Adrian-Amoddio/wildlife-detection-camera-system/object_detection/runs/detect/pi_demo/bird3.jpg

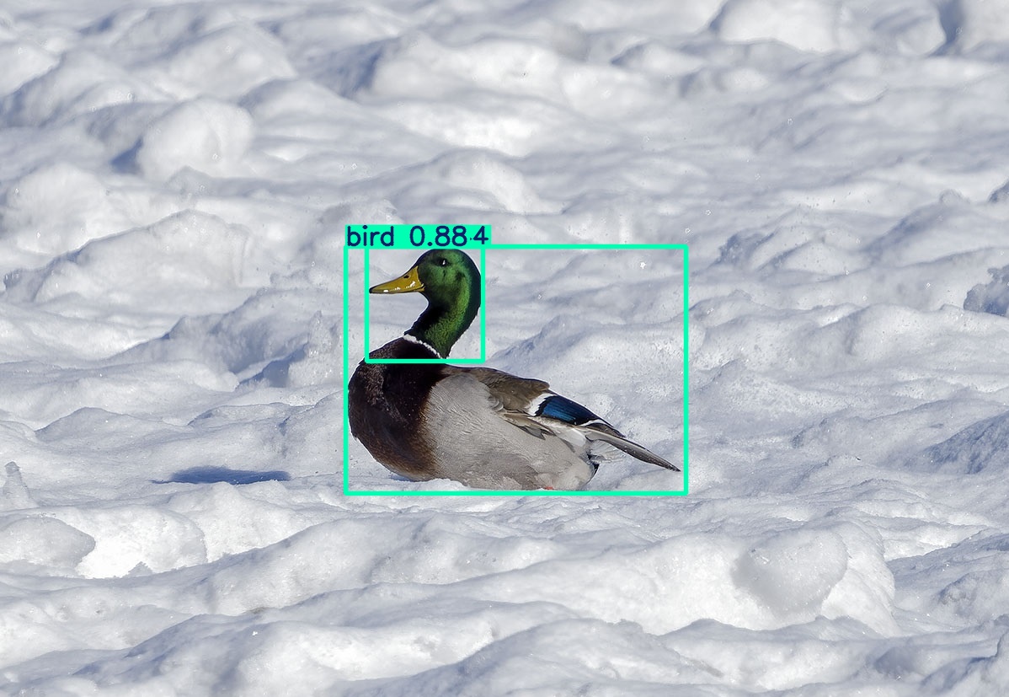
object_detection/runs/detect/pi_demo/bird3.jpg
