Adrian-Amoddio/wildlife-detection-camera-system/object_detection/runs/detect/pi_demo/bird.jpg

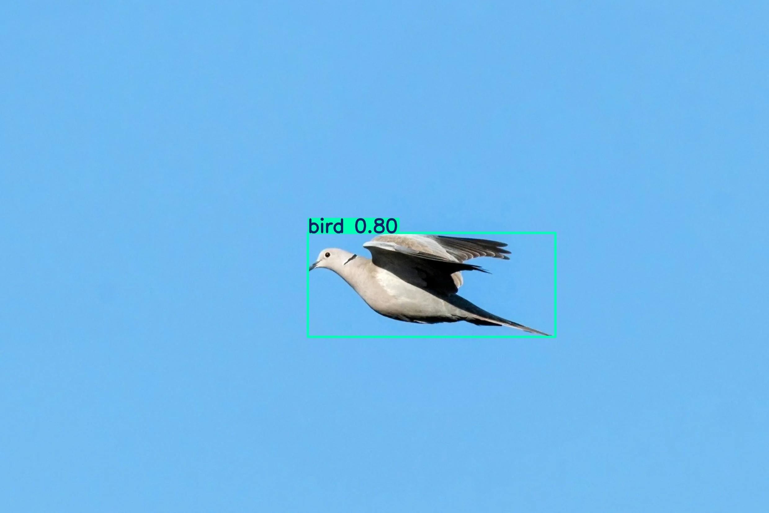
object_detection/runs/detect/pi_demo/bird.jpg
