Adrian-Amoddio/wildlife-detection-camera-system/object_detection/samples/dog.webp

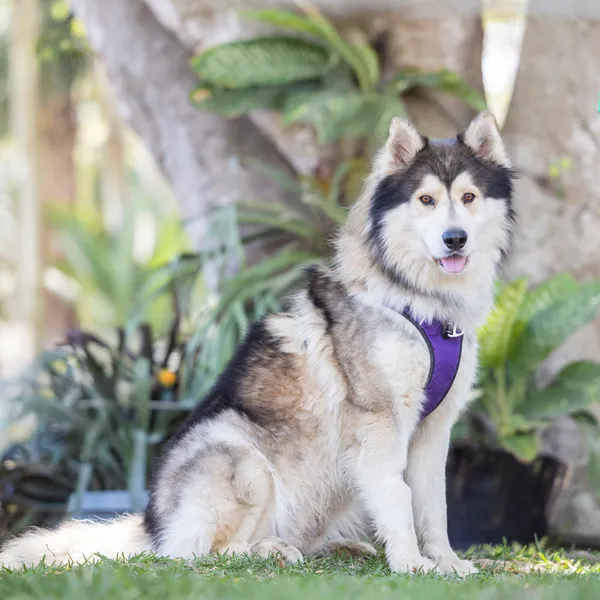
object_detection/samples/dog.webp
