Adrian-Amoddio/wildlife-detection-camera-system/docs/build-images/1.jpg

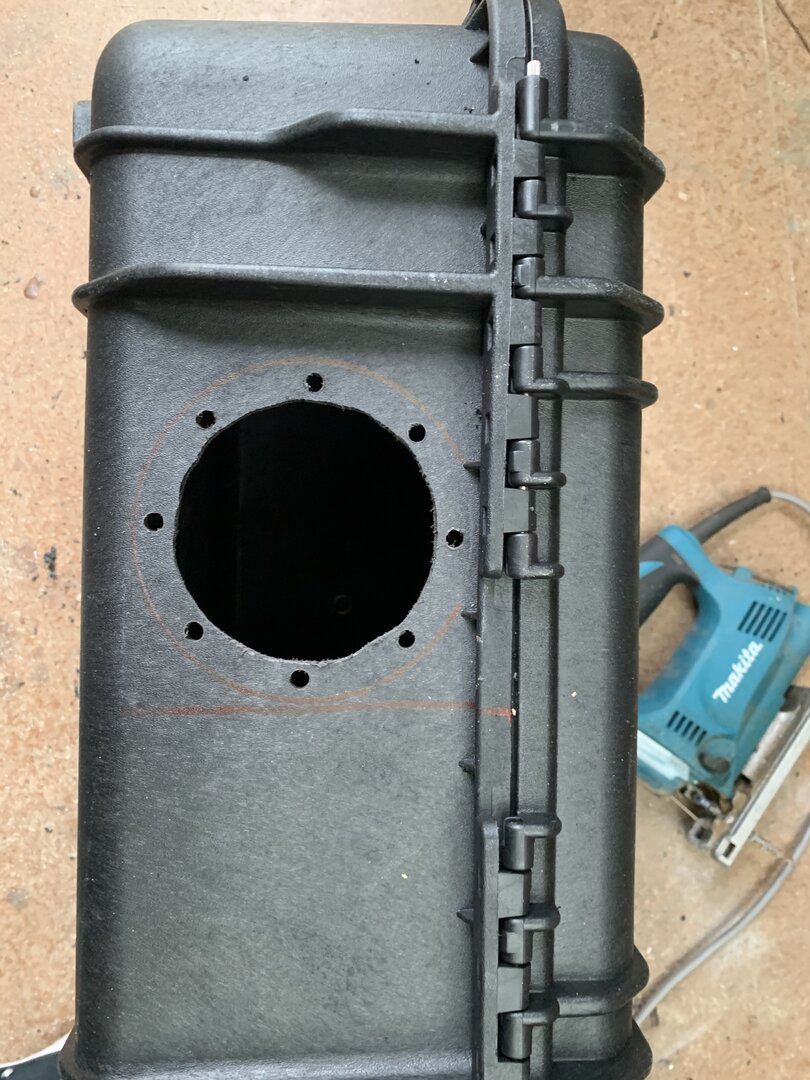
docs/build-images/1.jpg
