Adrian-Amoddio/wildlife-detection-camera-system/docs/build-images/2.jpg

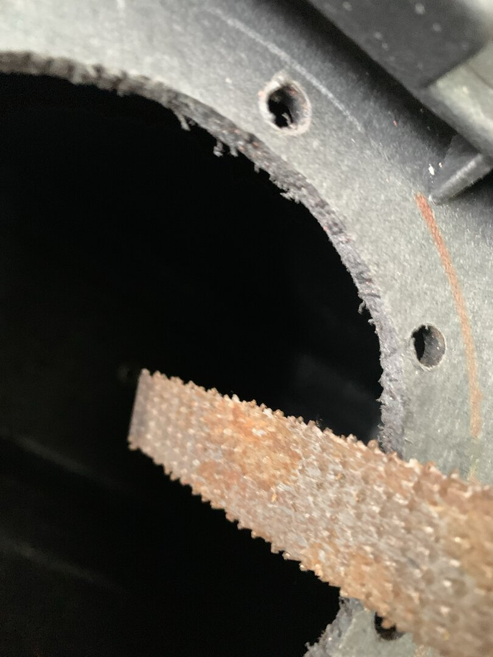
docs/build-images/2.jpg
