Adrian-Amoddio/wildlife-detection-camera-system/docs/build-images/3.jpg

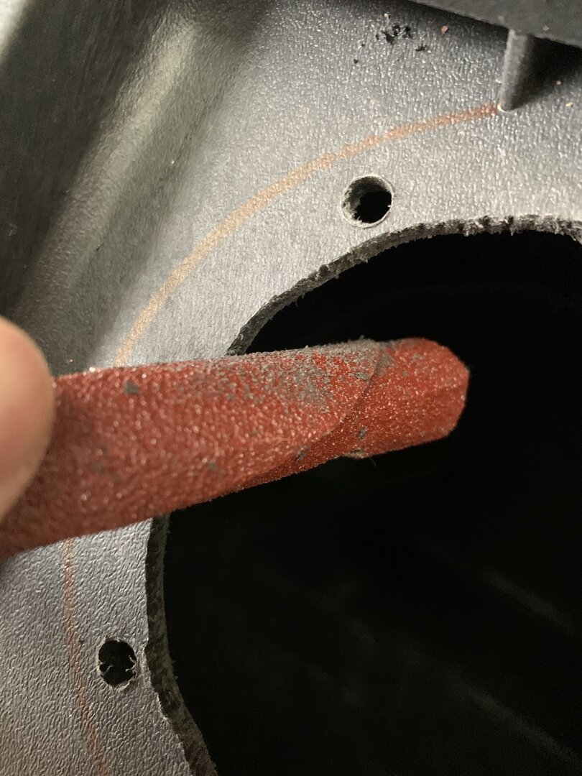
docs/build-images/3.jpg
