Adrian-Amoddio/wildlife-detection-camera-system/docs/build-images/4.jpg

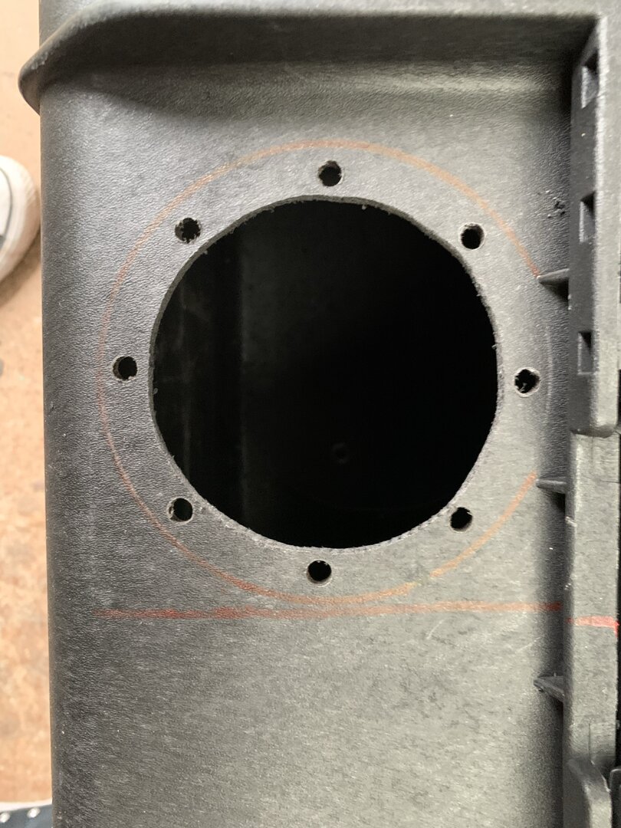
docs/build-images/4.jpg
