Adrian-Amoddio/wildlife-detection-camera-system/docs/build-images/6.jpg

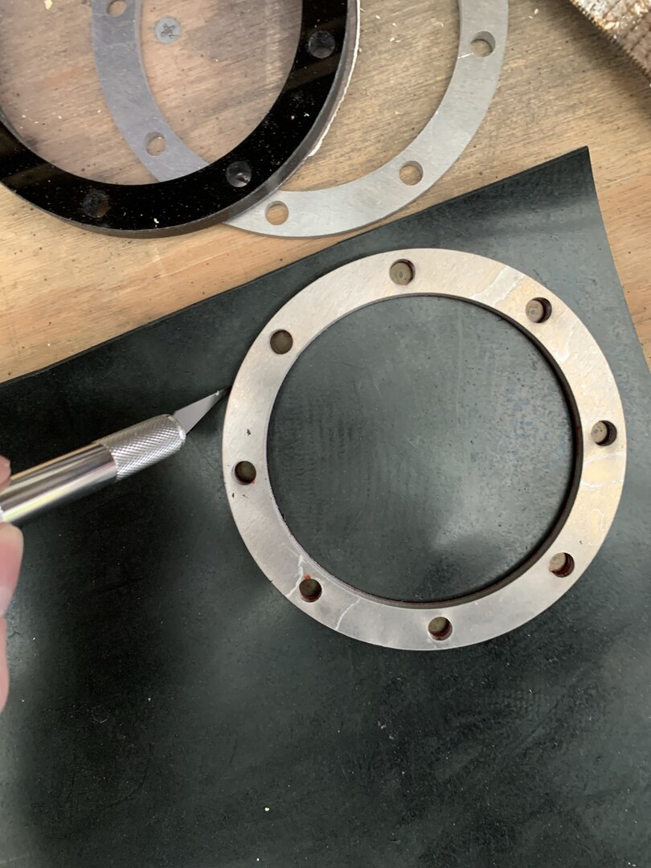
docs/build-images/6.jpg
