Adrian-Amoddio/wildlife-detection-camera-system/docs/build-images/7.jpg

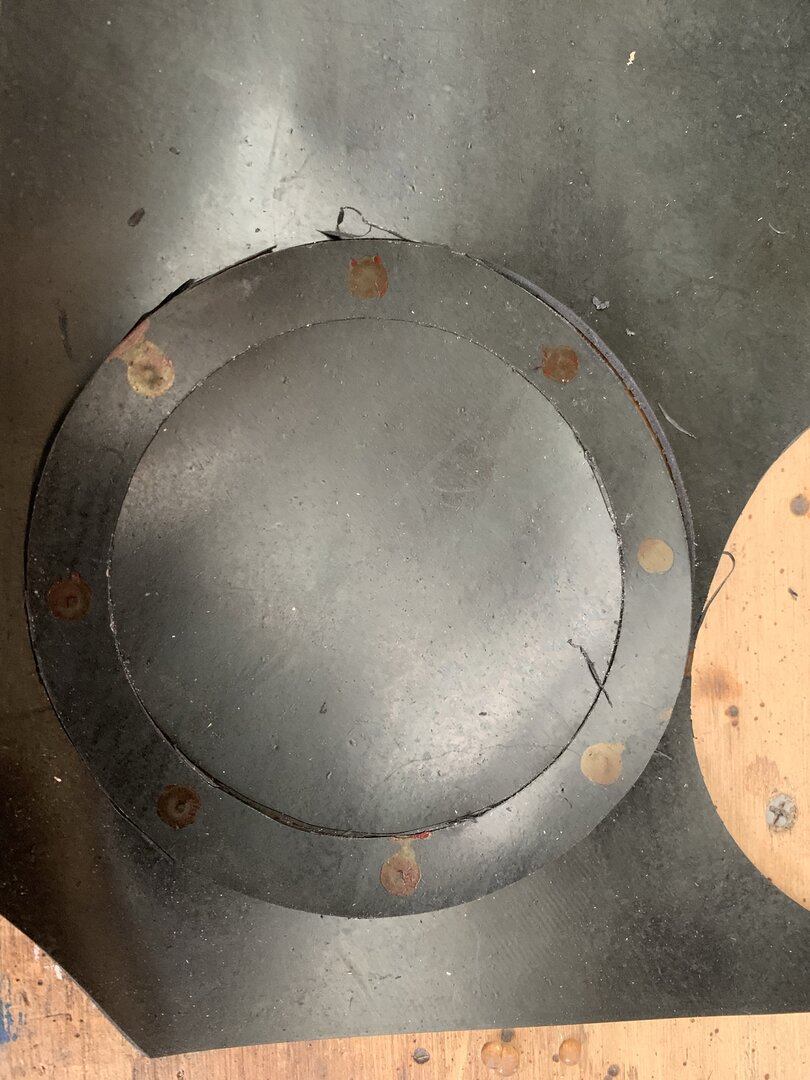
docs/build-images/7.jpg
