Adrian-Amoddio/wildlife-detection-camera-system/docs/build-images/8.jpg

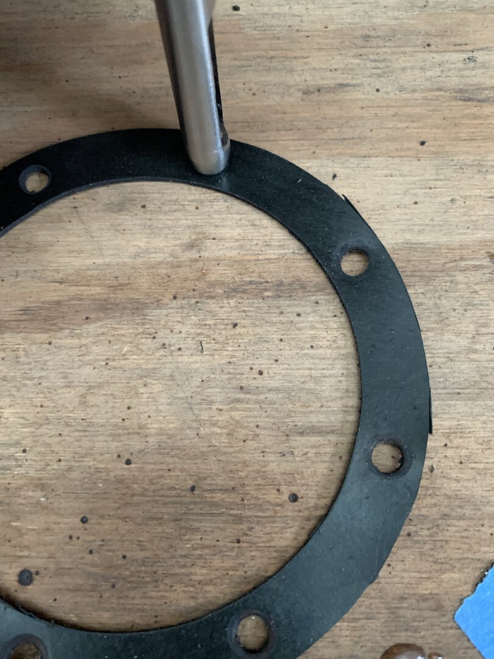
docs/build-images/8.jpg
