Adrian-Amoddio/wildlife-detection-camera-system/docs/build-images/9.jpg

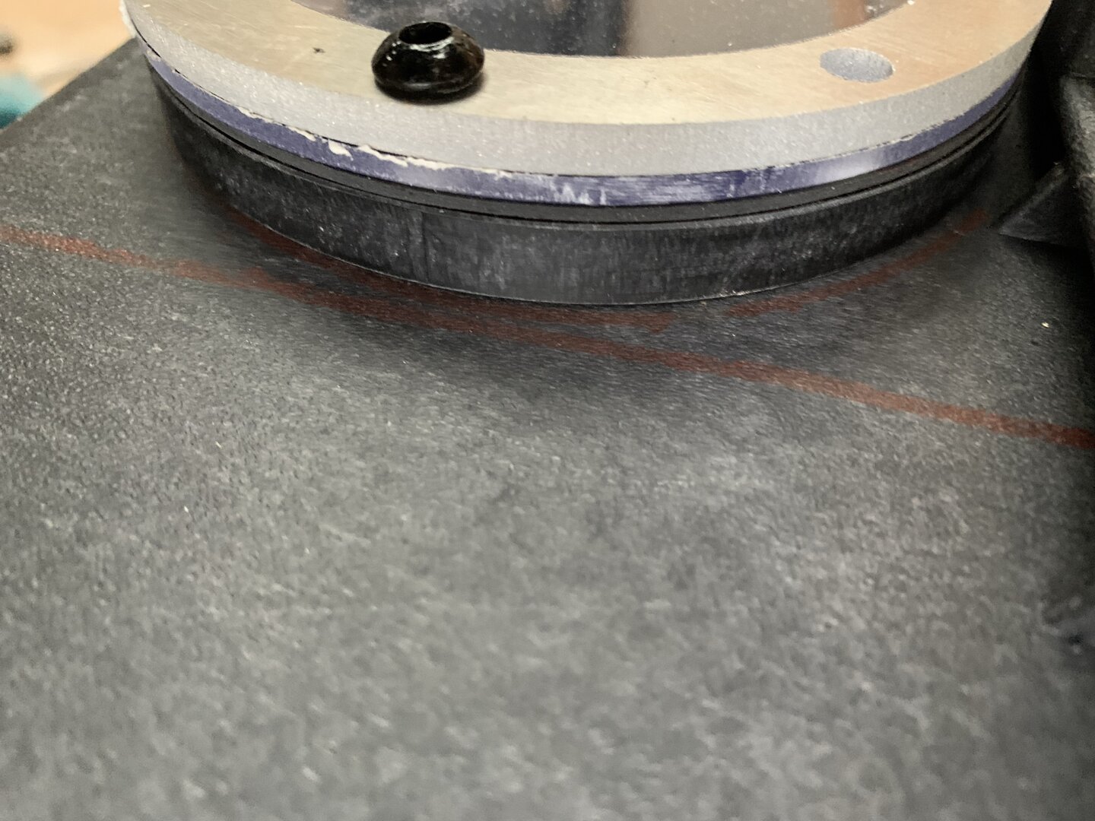
docs/build-images/9.jpg
