Adrian-Amoddio/wildlife-detection-camera-system/docs/build-images/10.jpg

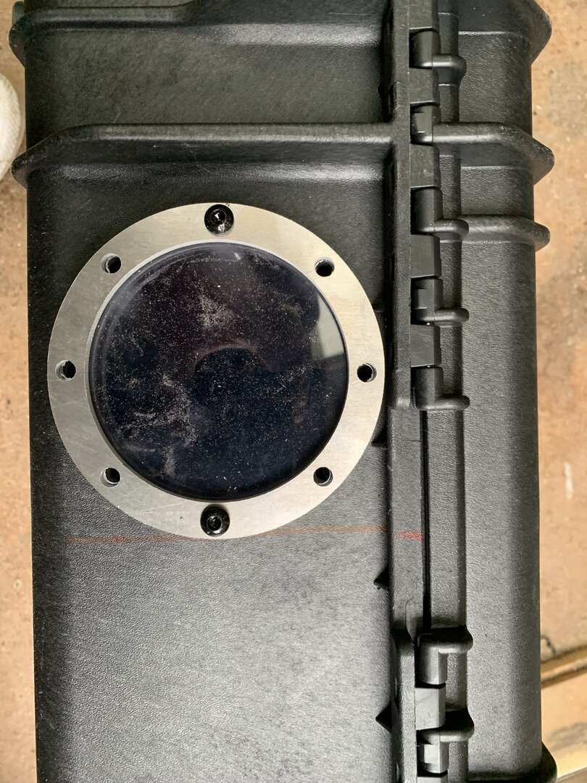
docs/build-images/10.jpg
