Adrian-Amoddio/wildlife-detection-camera-system/docs/build-images/11.jpg

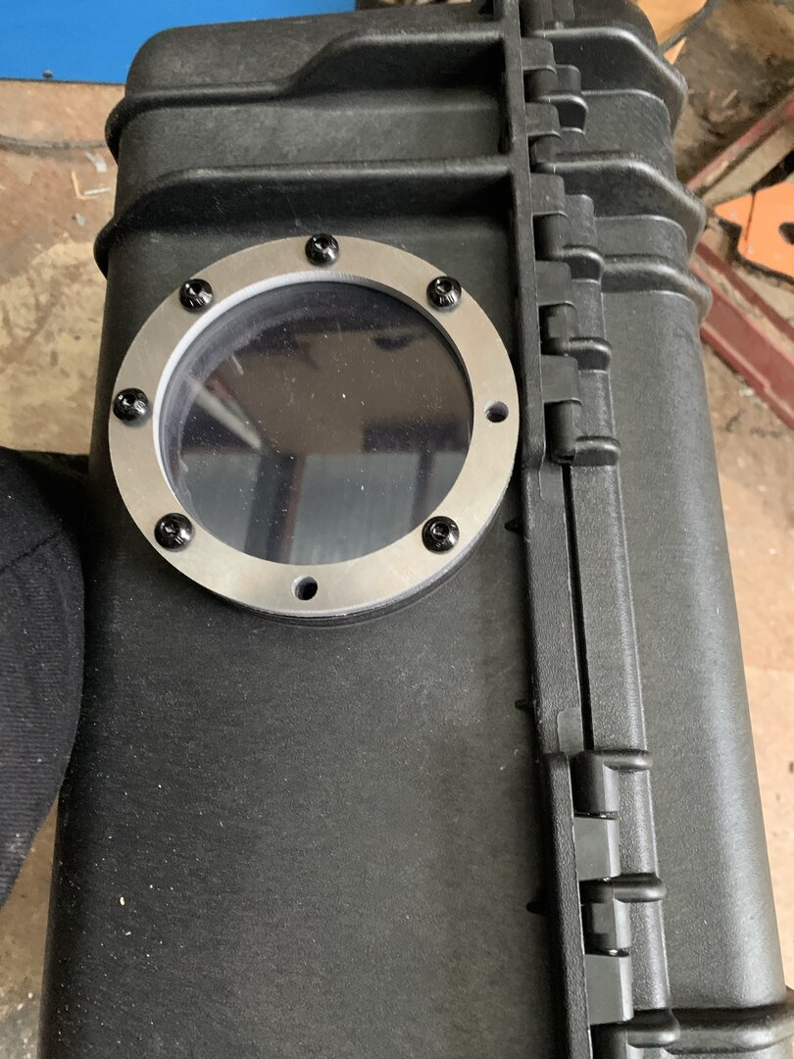
docs/build-images/11.jpg
