Adrian-Amoddio/wildlife-detection-camera-system/docs/build-images/12.jpg

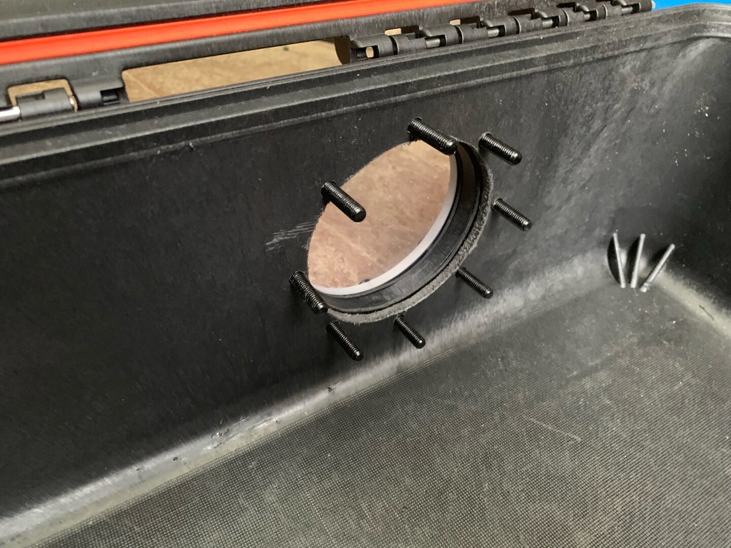
docs/build-images/12.jpg
