Adrian-Amoddio/wildlife-detection-camera-system/docs/build-images/17.jpg

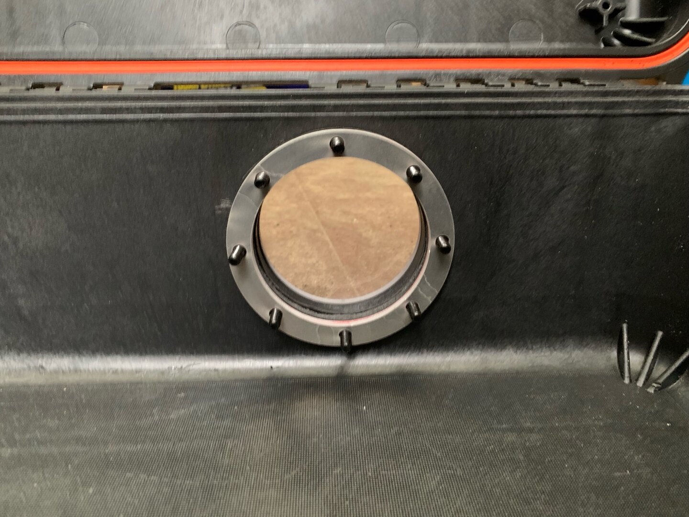
docs/build-images/17.jpg
