Adrian-Amoddio/wildlife-detection-camera-system/docs/build-images/18.jpg

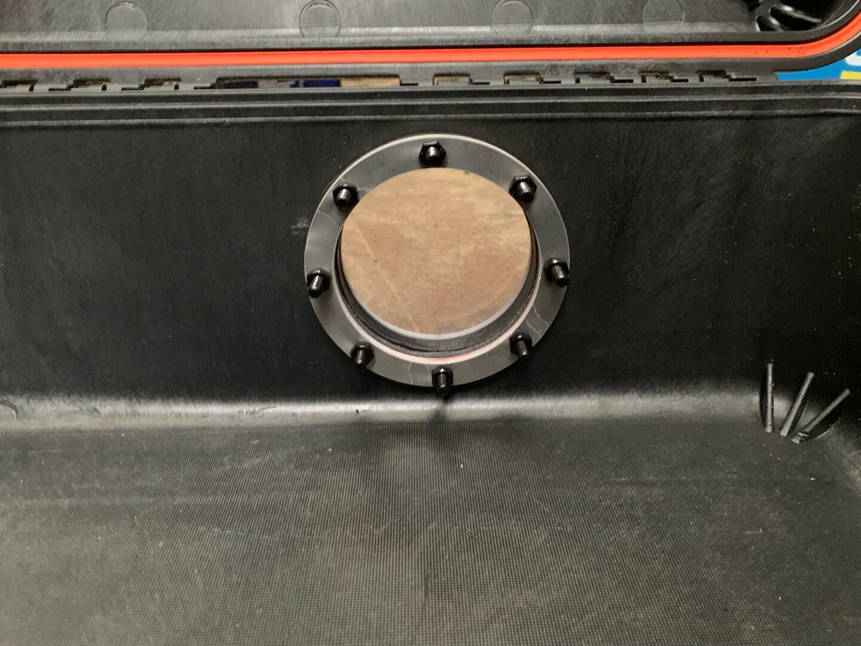
docs/build-images/18.jpg
