Adrian-Amoddio/wildlife-detection-camera-system/docs/build-images/19.jpg

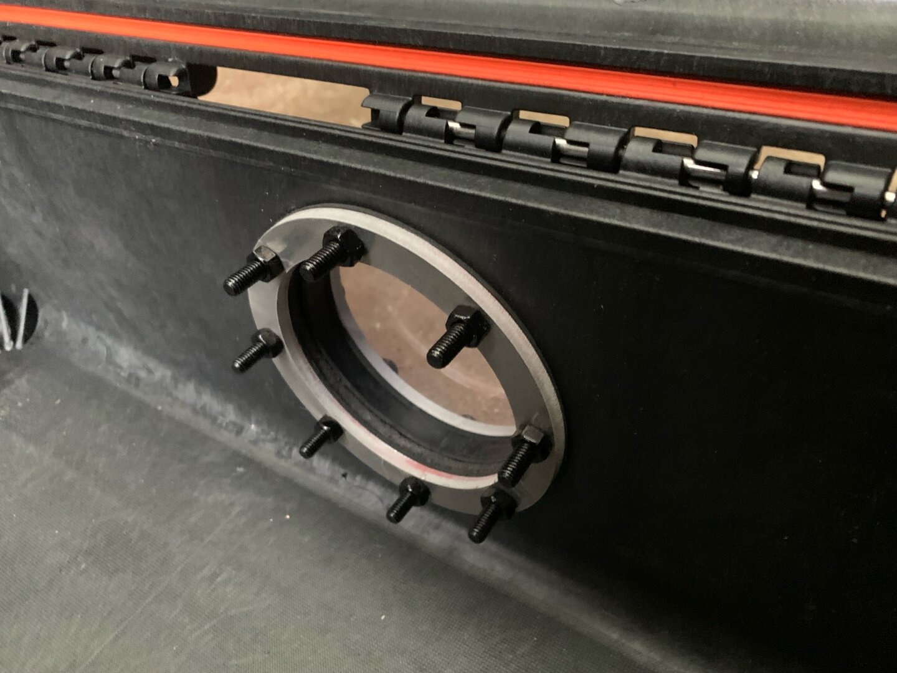
docs/build-images/19.jpg
