Adrian-Amoddio/wildlife-detection-camera-system/docs/build-images/21.jpg

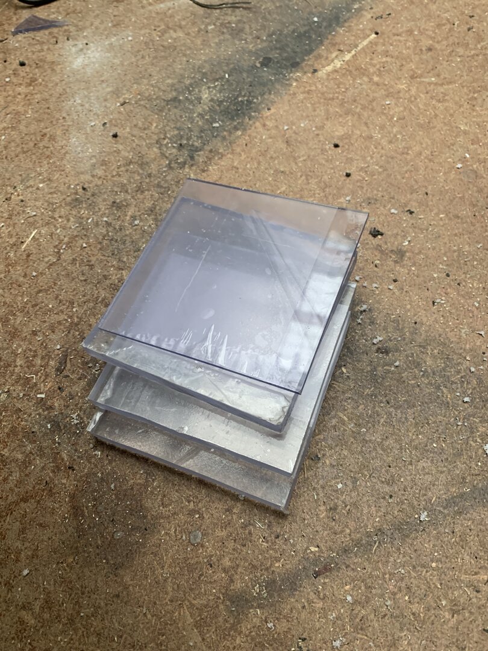
docs/build-images/21.jpg
