Adrian-Amoddio/wildlife-detection-camera-system/docs/build-images/22.jpg

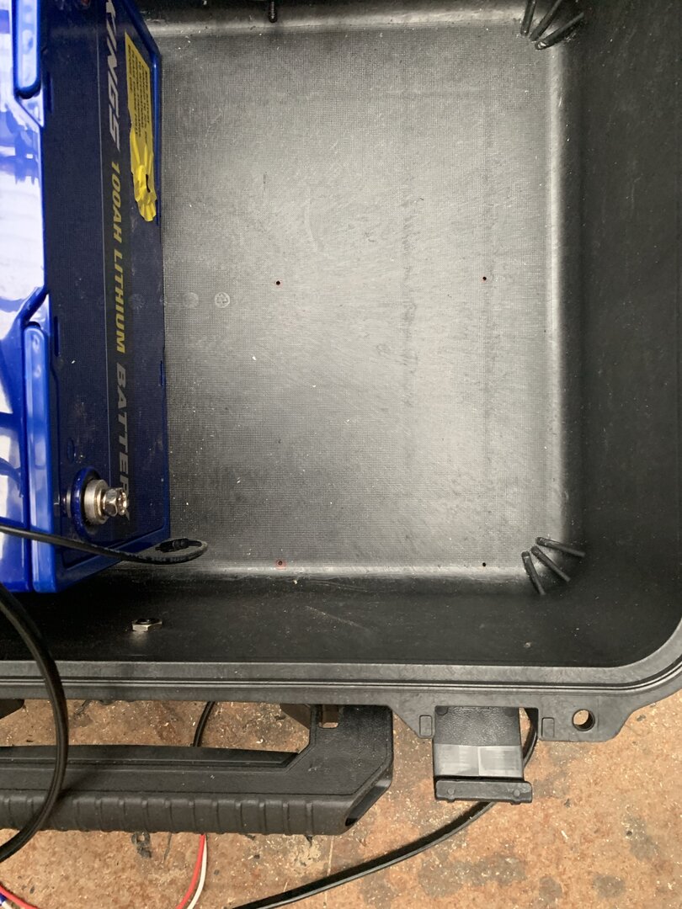
docs/build-images/22.jpg
