Adrian-Amoddio/wildlife-detection-camera-system/docs/build-images/24.jpg

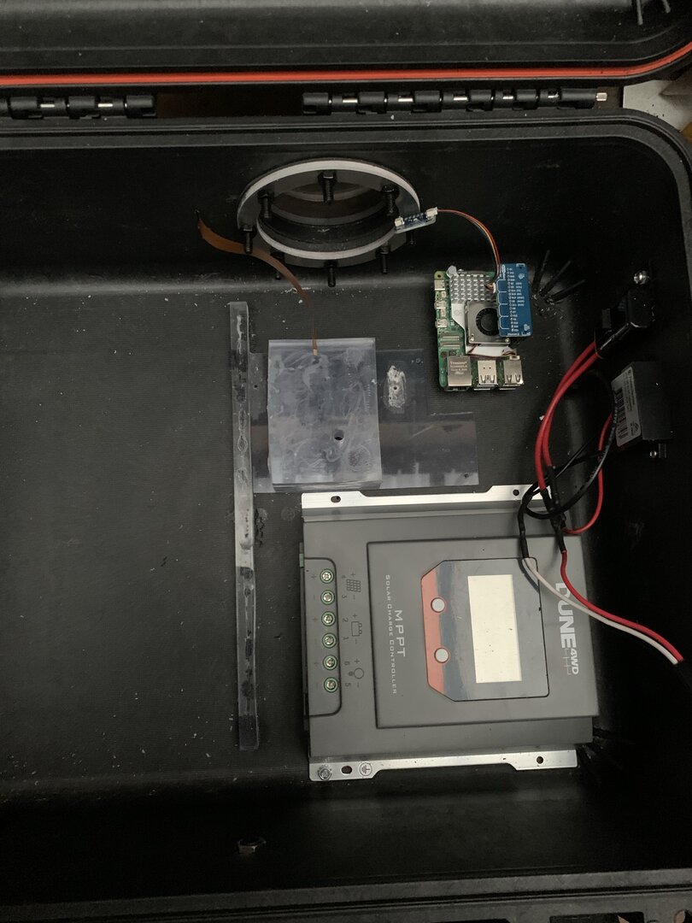
docs/build-images/24.jpg
