Adrian-Amoddio/wildlife-detection-camera-system/docs/build-images/25.jpg

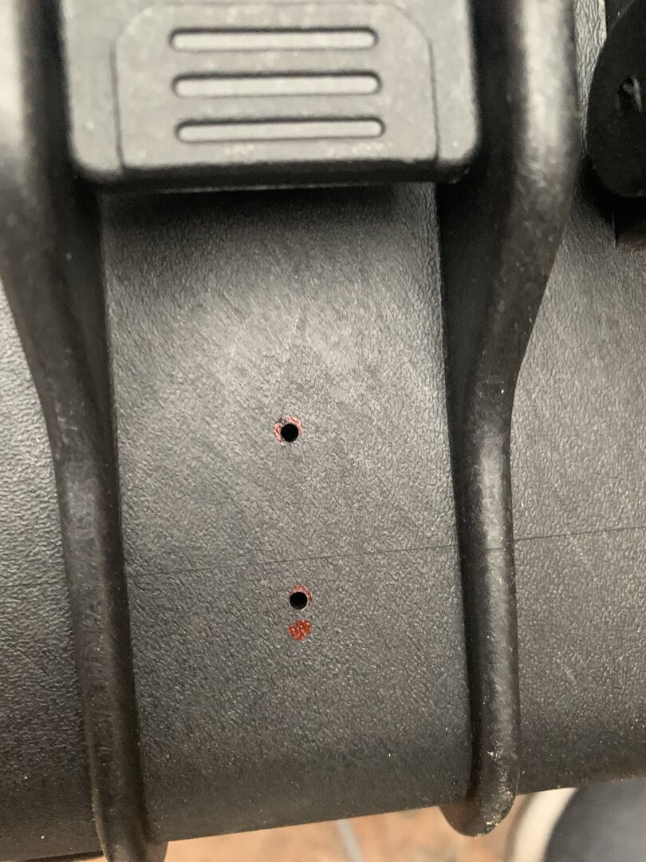
docs/build-images/25.jpg
