Adrian-Amoddio/wildlife-detection-camera-system/docs/build-images/26.jpg

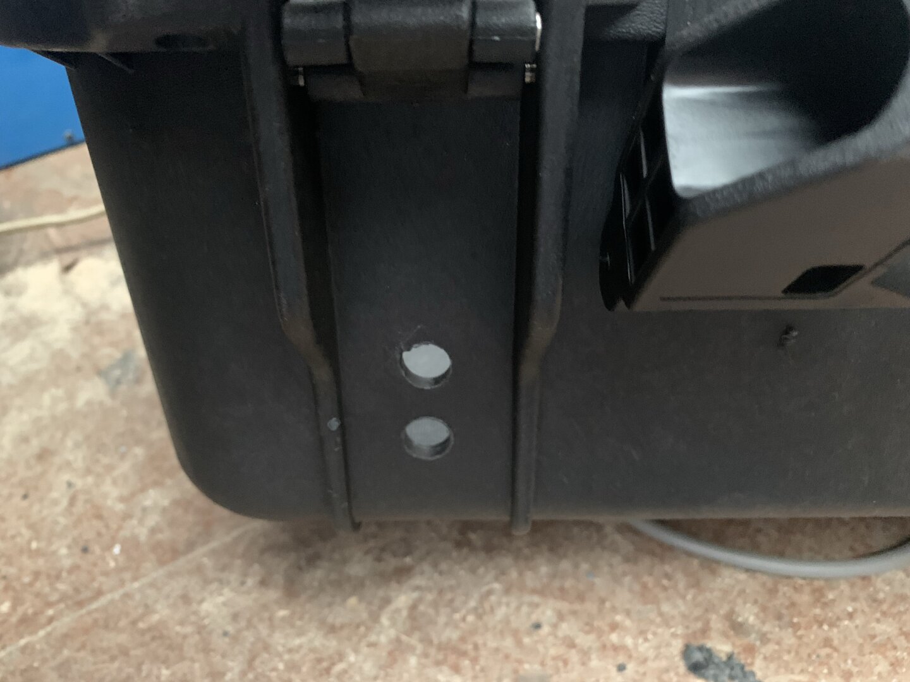
docs/build-images/26.jpg
