Adrian-Amoddio/wildlife-detection-camera-system/docs/build-images/27.jpg

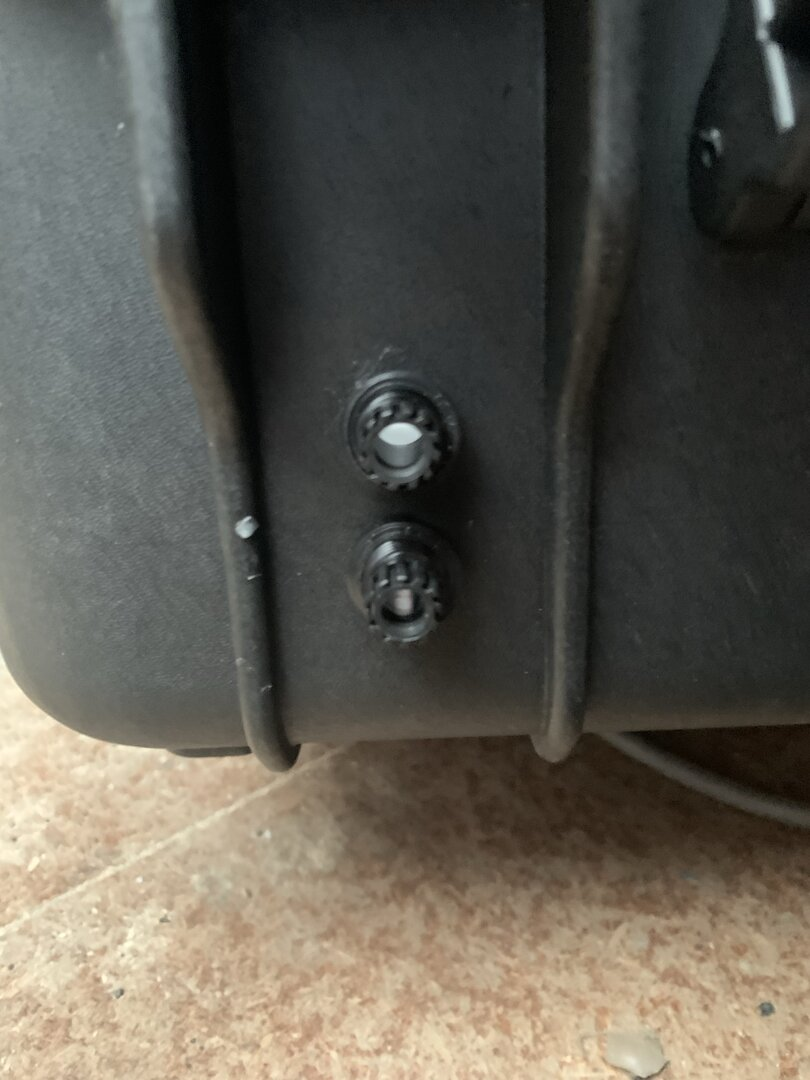
docs/build-images/27.jpg
