Adrian-Amoddio/wildlife-detection-camera-system/docs/build-images/28.jpg

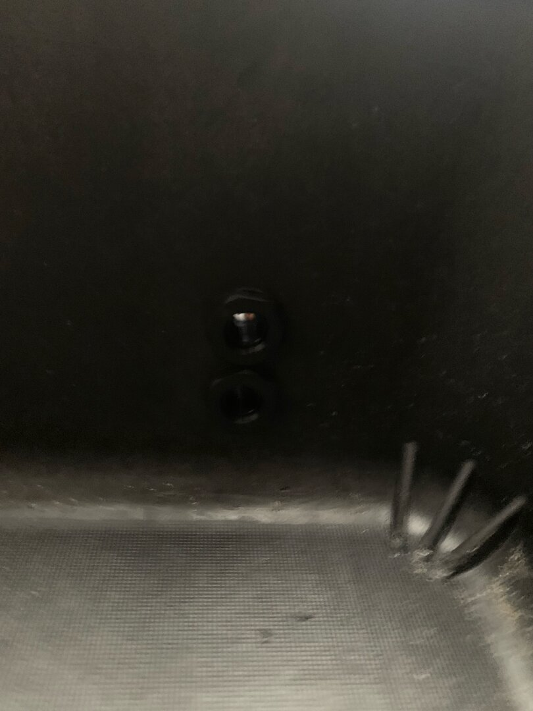
docs/build-images/28.jpg
