Adrian-Amoddio/wildlife-detection-camera-system/docs/build-images/29.jpg

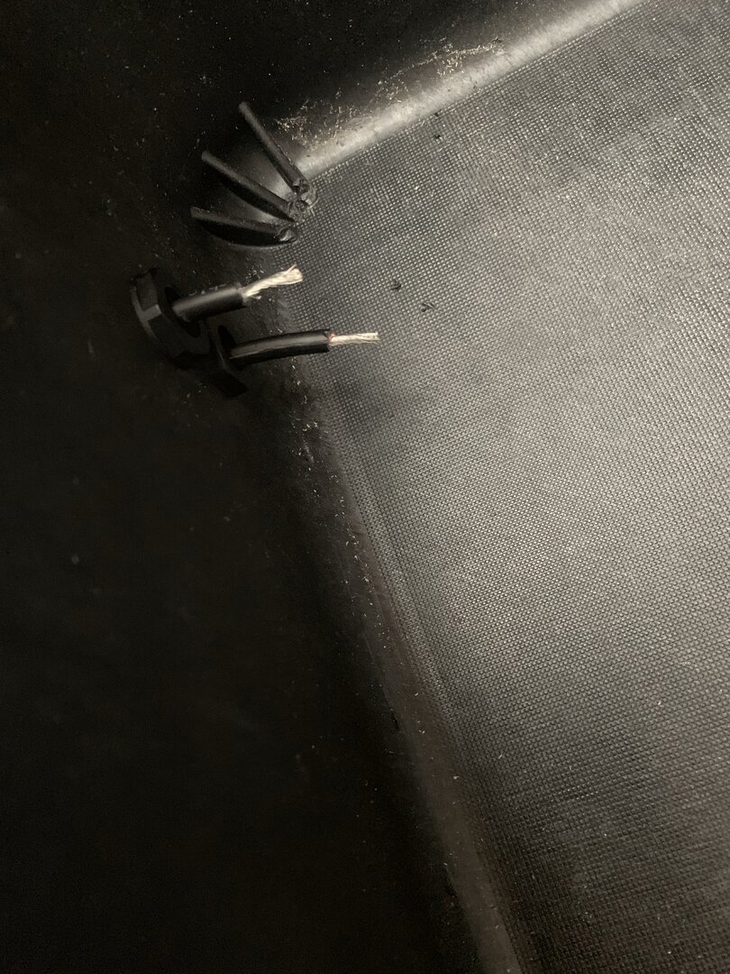
docs/build-images/29.jpg
