Adrian-Amoddio/wildlife-detection-camera-system/docs/build-images/30.jpg

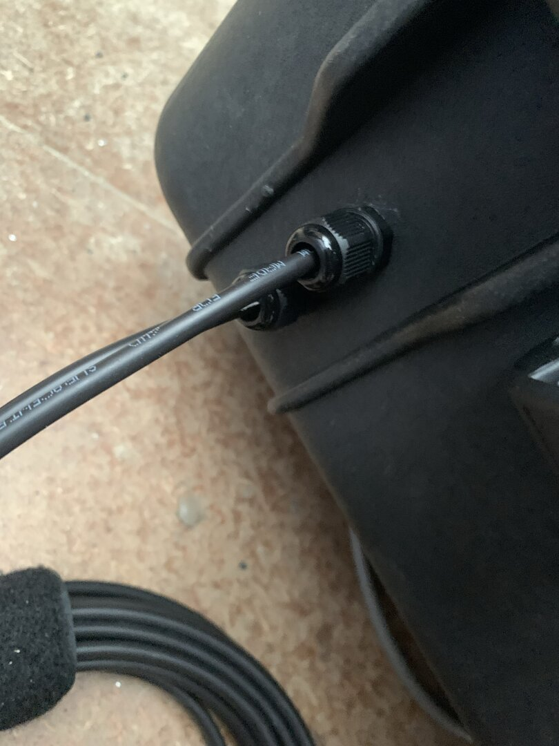
docs/build-images/30.jpg
