Adrian-Amoddio/wildlife-detection-camera-system/docs/build-images/31.jpg

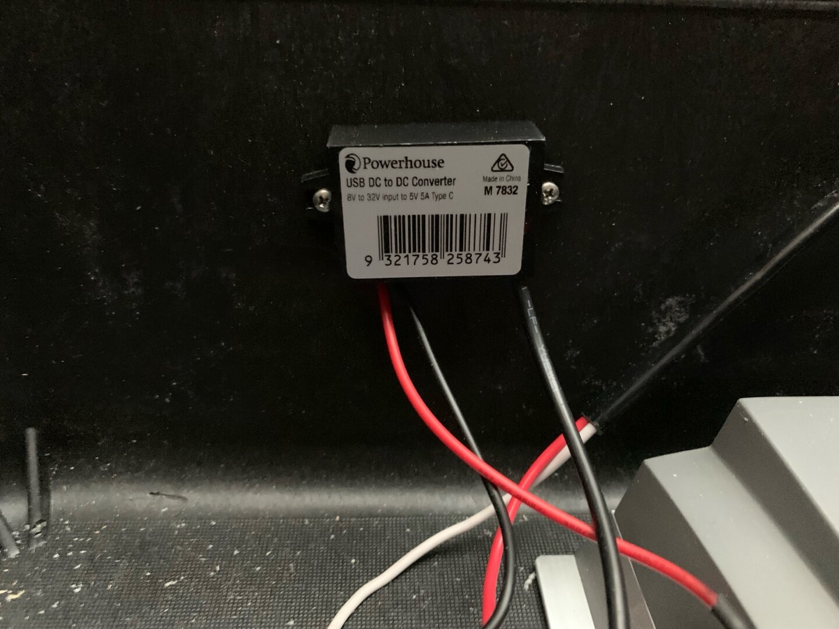
docs/build-images/31.jpg
