Adrian-Amoddio/wildlife-detection-camera-system/docs/build-images/34.jpg

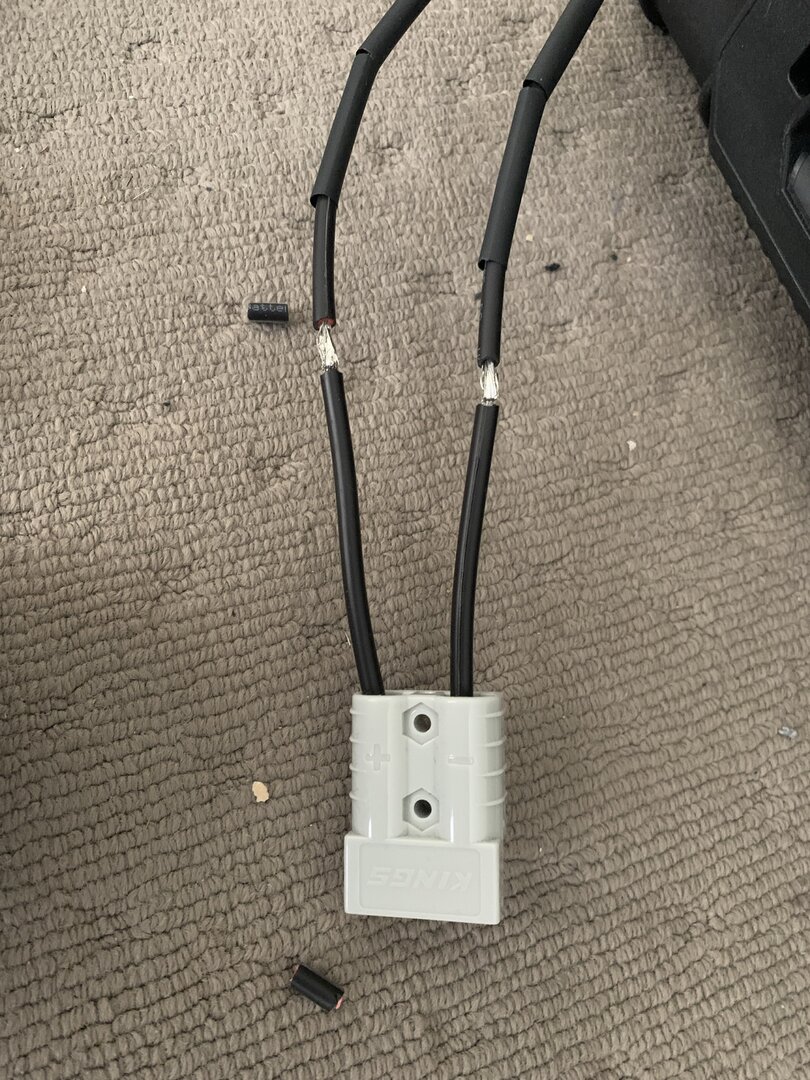
docs/build-images/34.jpg
