Adrian-Amoddio/wildlife-detection-camera-system/docs/build-images/35.jpg

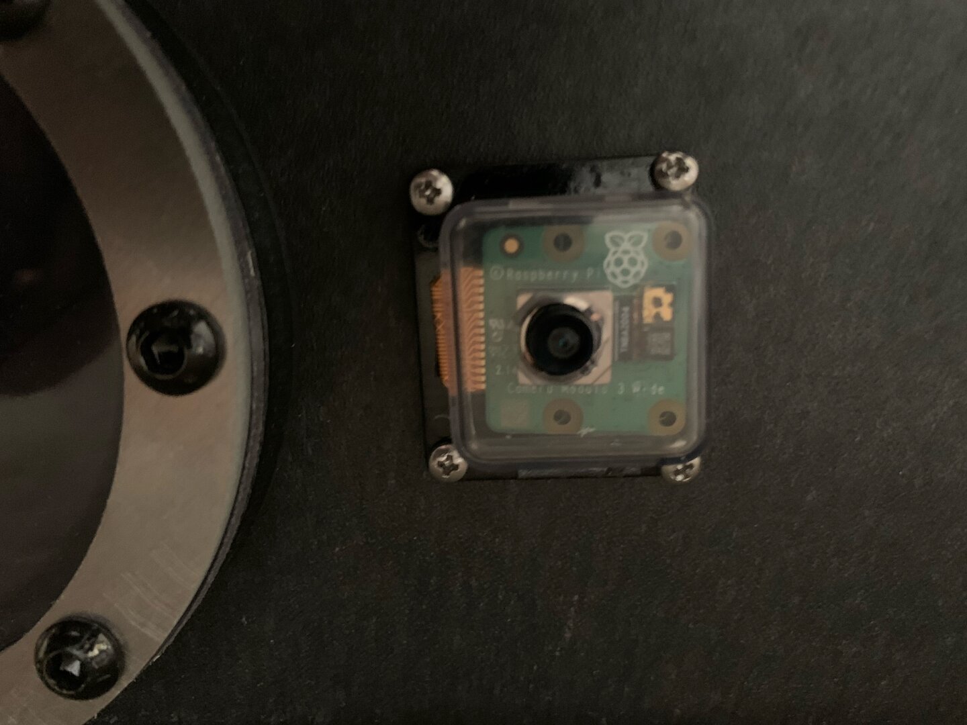
docs/build-images/35.jpg
