Adrian-Amoddio/wildlife-detection-camera-system/docs/build-images/36.jpg

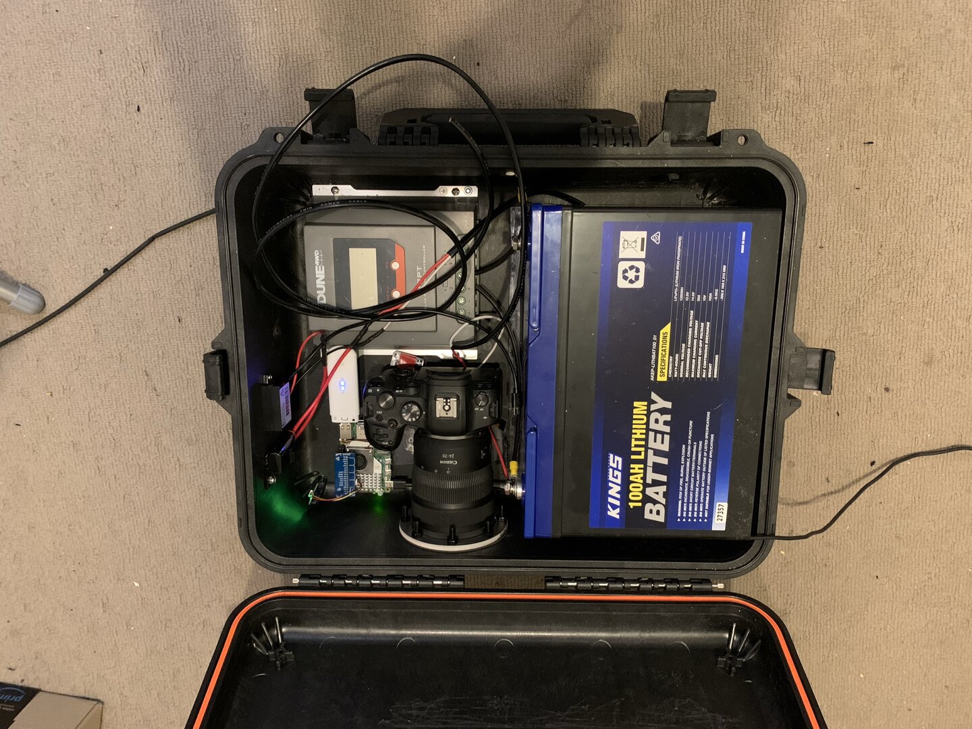
docs/build-images/36.jpg
