Adrian-Amoddio/wildlife-detection-camera-system/docs/build-images/37.jpg

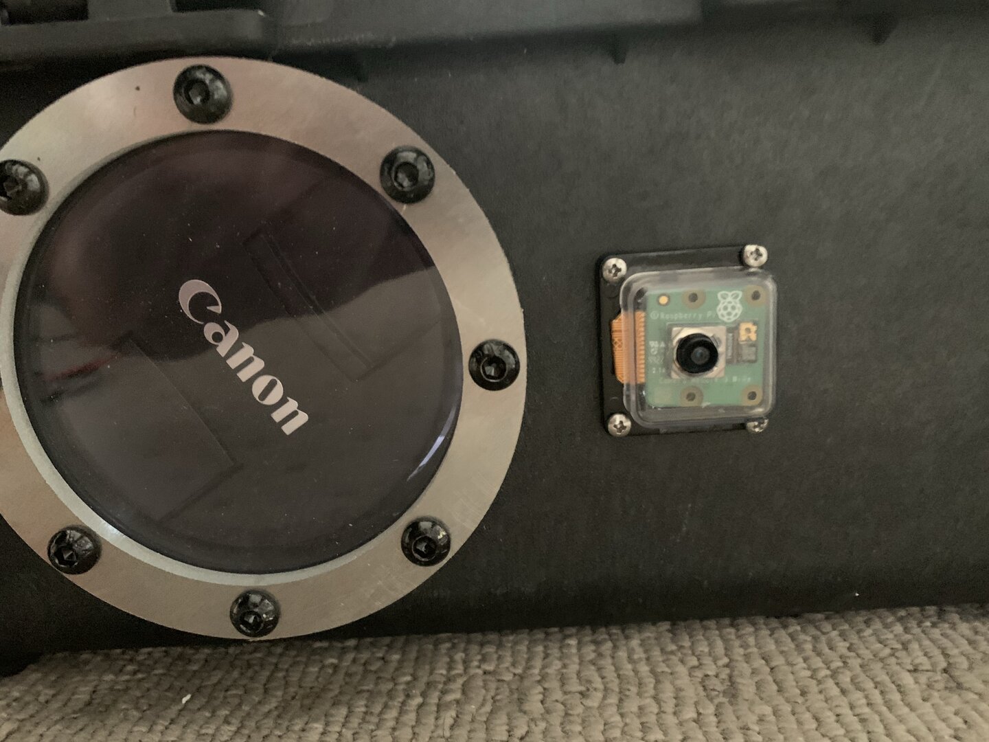
docs/build-images/37.jpg
