Adrian-Amoddio/wildlife-detection-camera-system/docs/build-images/38.jpg

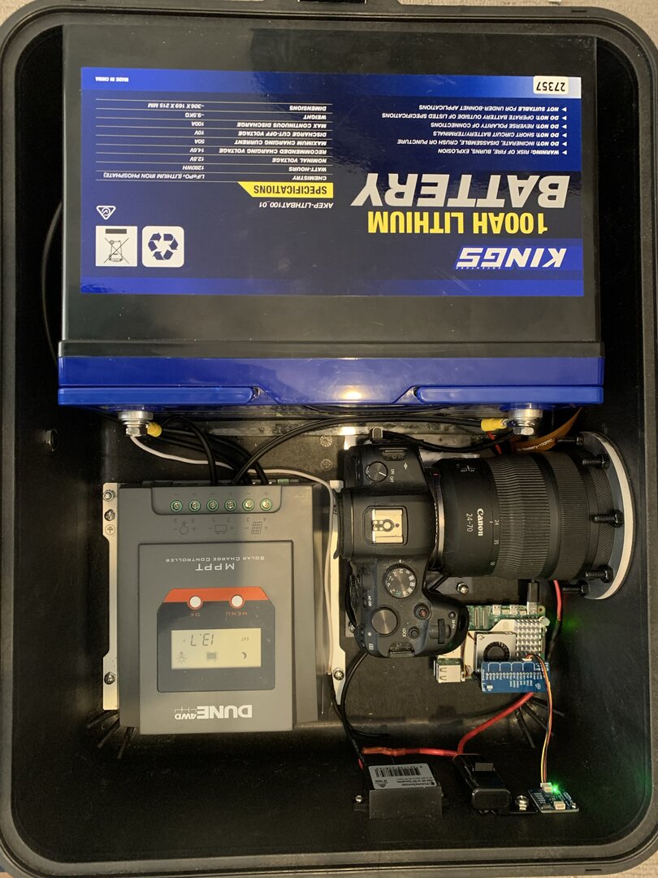
docs/build-images/38.jpg
