Adrian-Amoddio/wildlife-detection-camera-system/docs/build-images/39.jpg

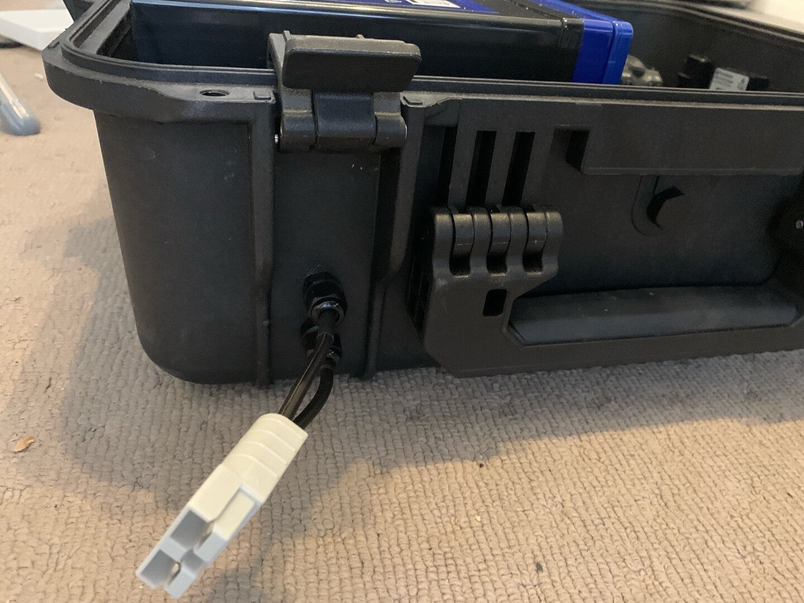
docs/build-images/39.jpg
