Adrian-Amoddio/wildlife-detection-camera-system/docs/build-images/40.jpg

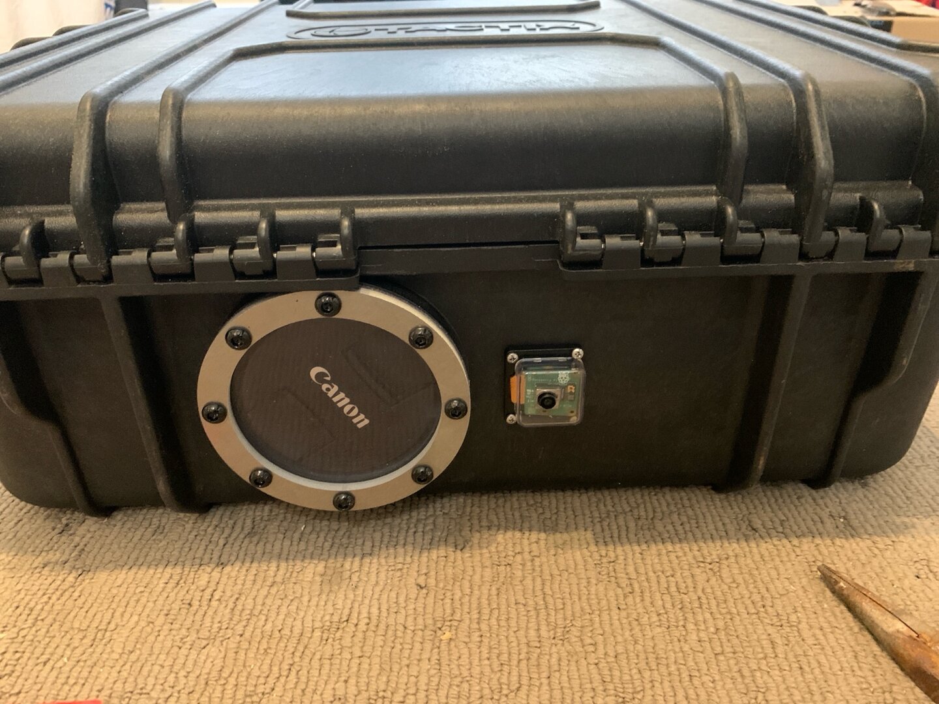
docs/build-images/40.jpg
